JellyTitan/Sofle-Pico/docs/images/qmk/sofle_pico_hero_image.jpeg

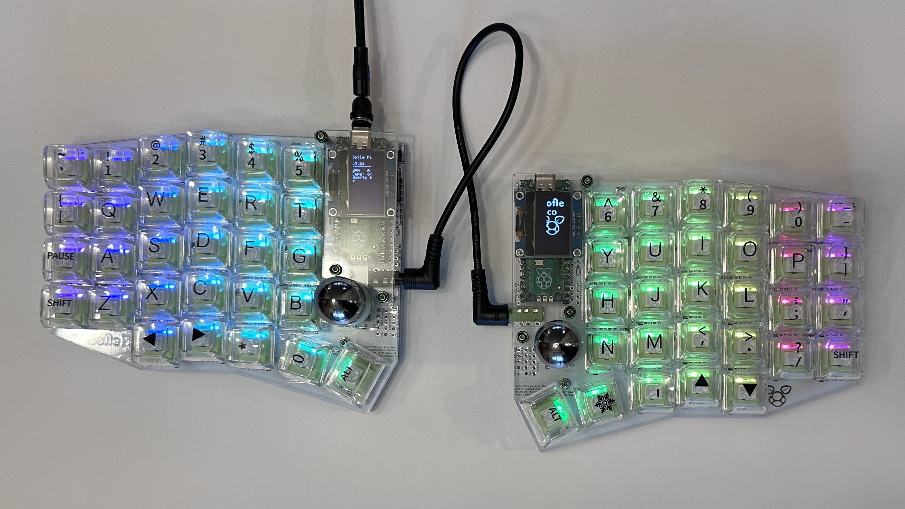
docs/images/qmk/sofle_pico_hero_image.jpeg
