JellyTitan/Sofle-Pico/docs/images/pcba_ordering_images/pcba_1.png

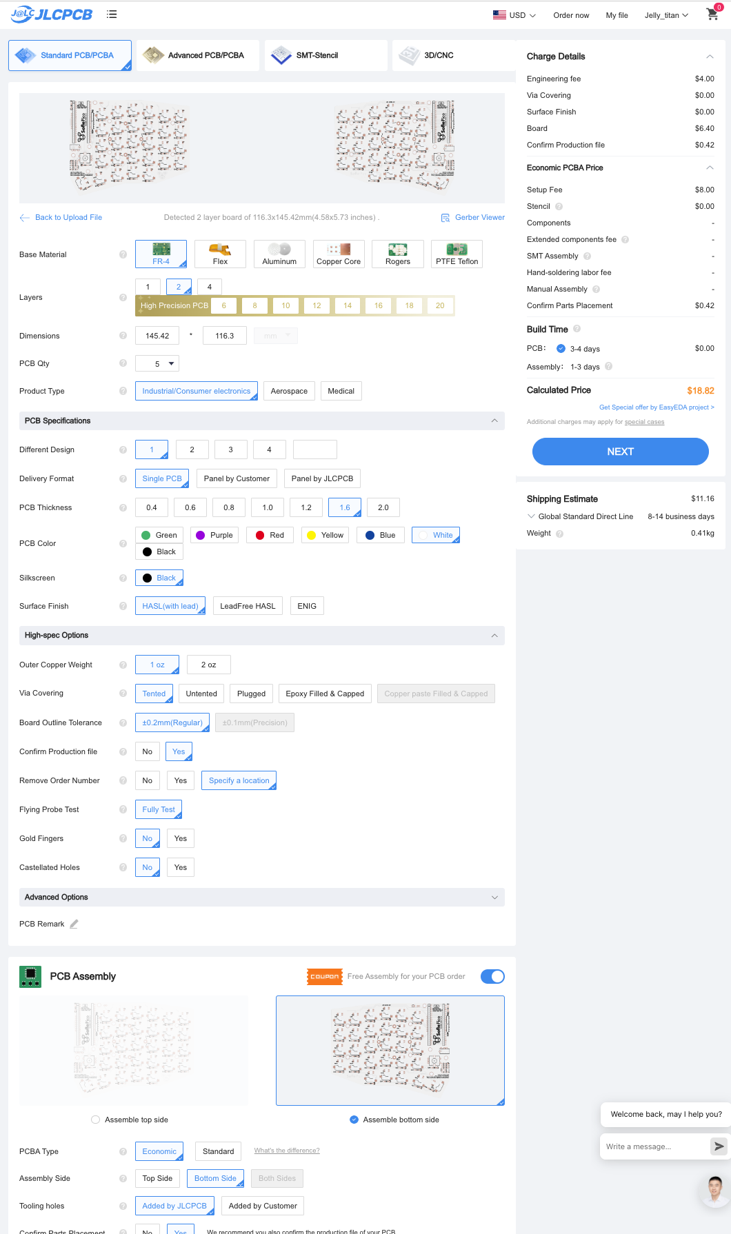
docs/images/pcba_ordering_images/pcba_1.png
