JellyTitan/Sofle-Pico/docs/images/pcba_ordering_images/pcba_3.png

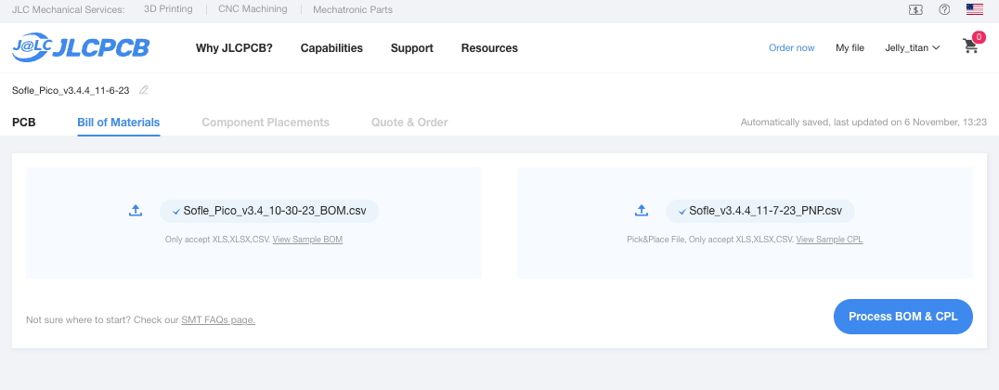
docs/images/pcba_ordering_images/pcba_3.png
