JellyTitan/Sofle-Pico/docs/images/pcba_ordering_images/pcba_4.png

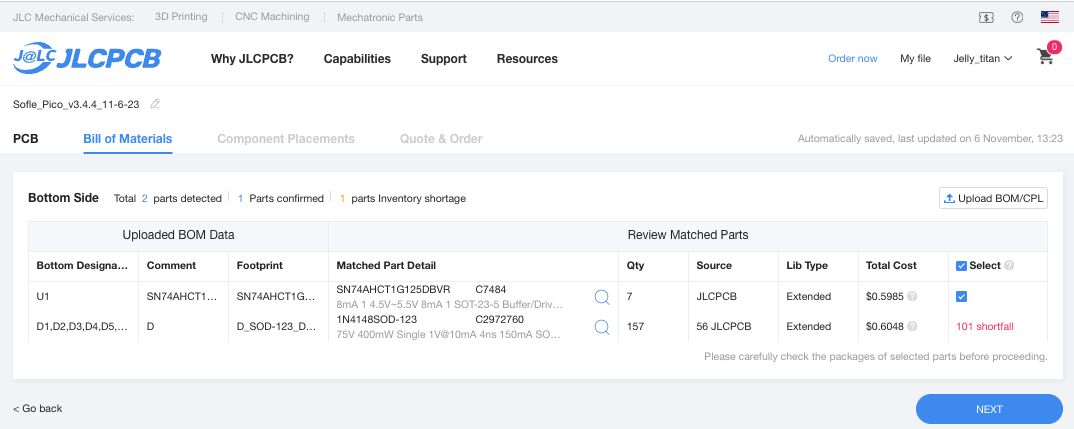
docs/images/pcba_ordering_images/pcba_4.png
