JellyTitan/Sofle-Pico/docs/images/pcba_ordering_images/pcba_5.png

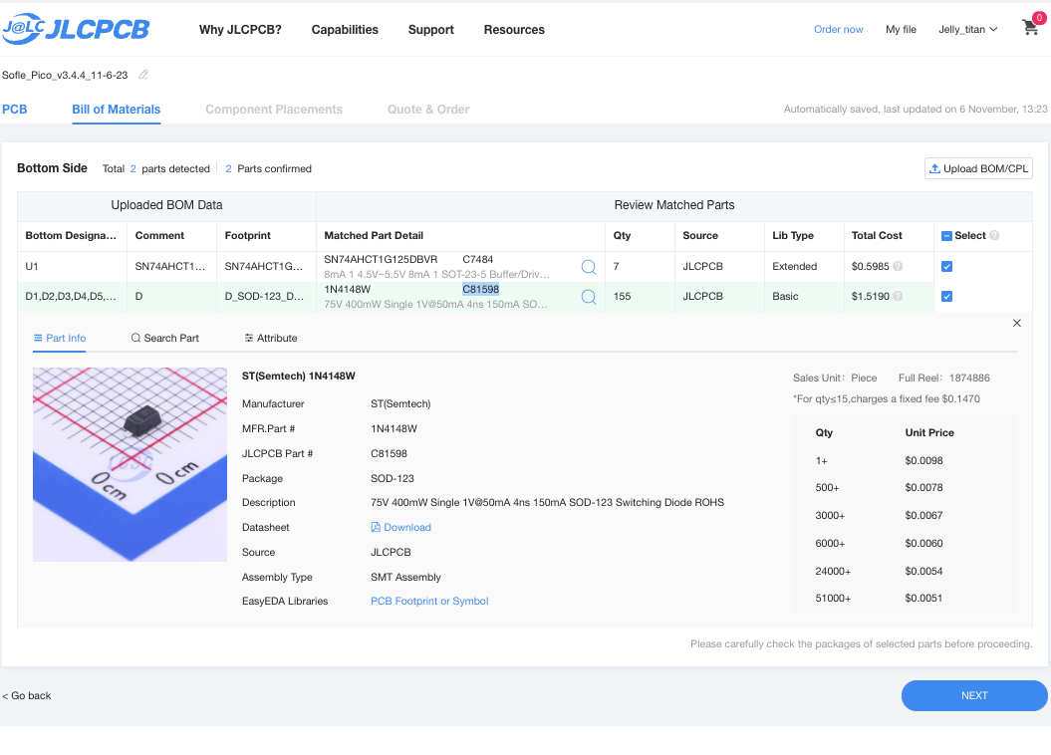
docs/images/pcba_ordering_images/pcba_5.png
