JellyTitan/Sofle-Pico/docs/images/pcba_ordering_images/pcba_6.png

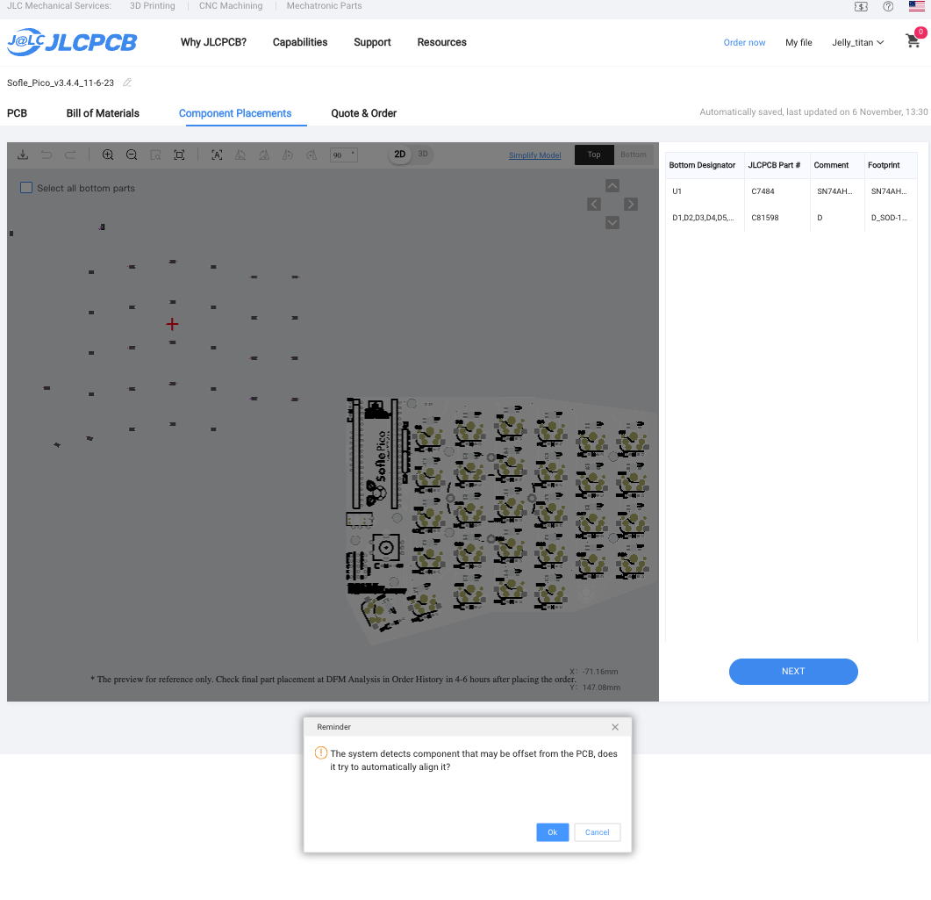
docs/images/pcba_ordering_images/pcba_6.png
