JellyTitan/Sofle-Pico/docs/images/pcba_ordering_images/pcba_7.png

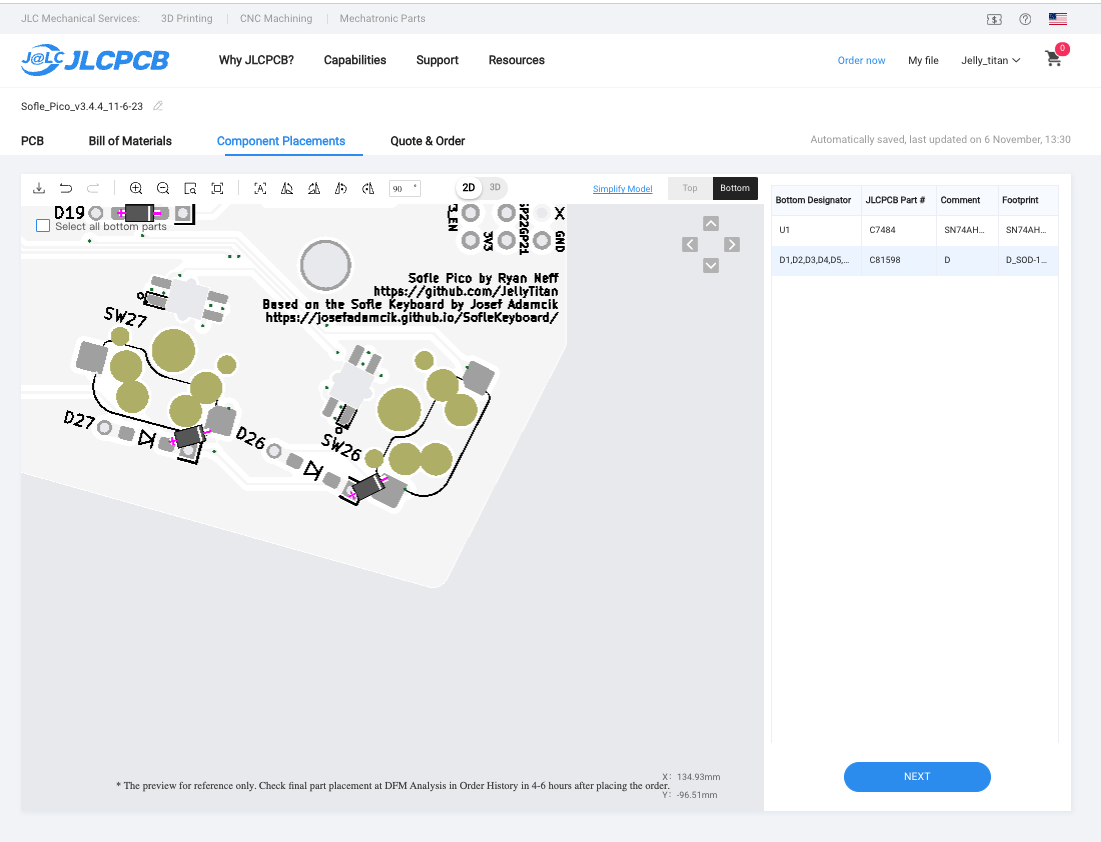
docs/images/pcba_ordering_images/pcba_7.png
