JellyTitan/Sofle-Pico/docs/images/pcba_ordering_images/pcba_8.png

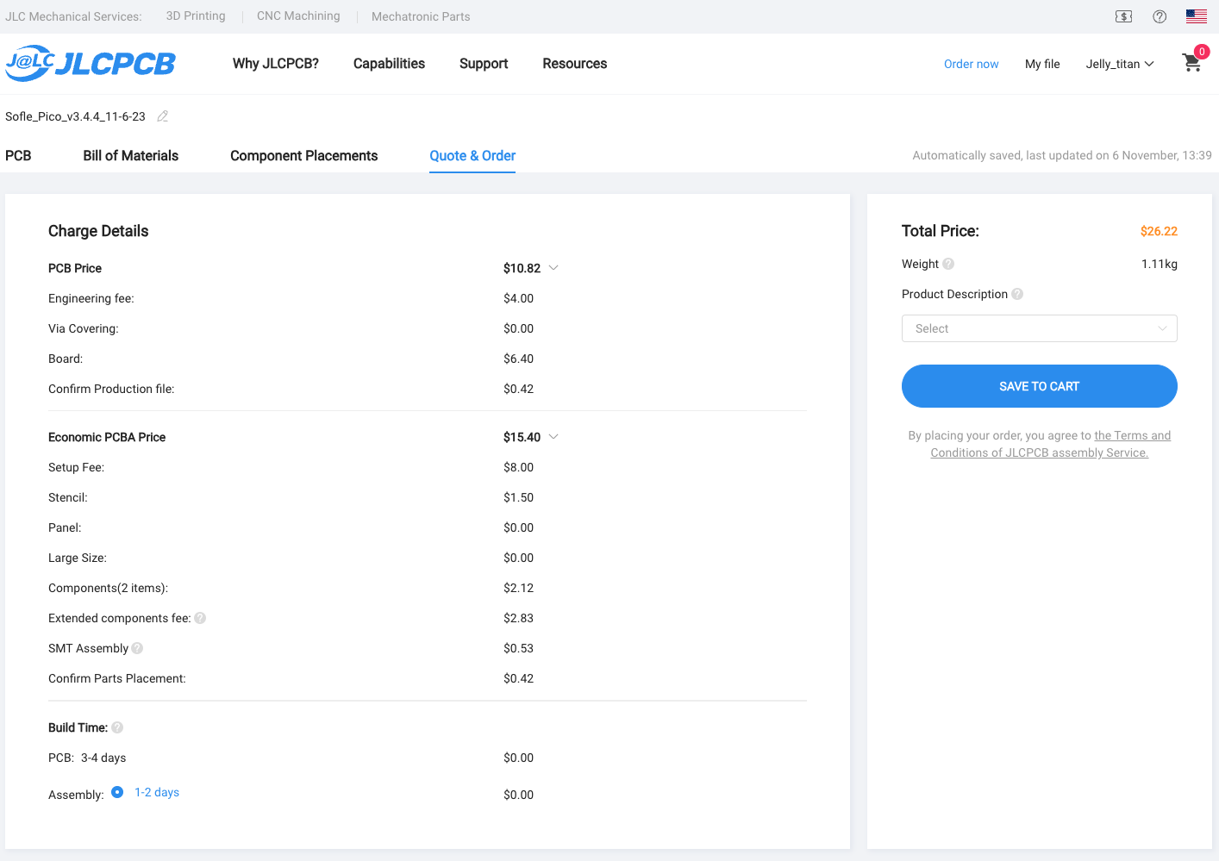
docs/images/pcba_ordering_images/pcba_8.png
