JellyTitan/Sofle-Pico/docs/images/pcba_ordering_images/pcba_9.png

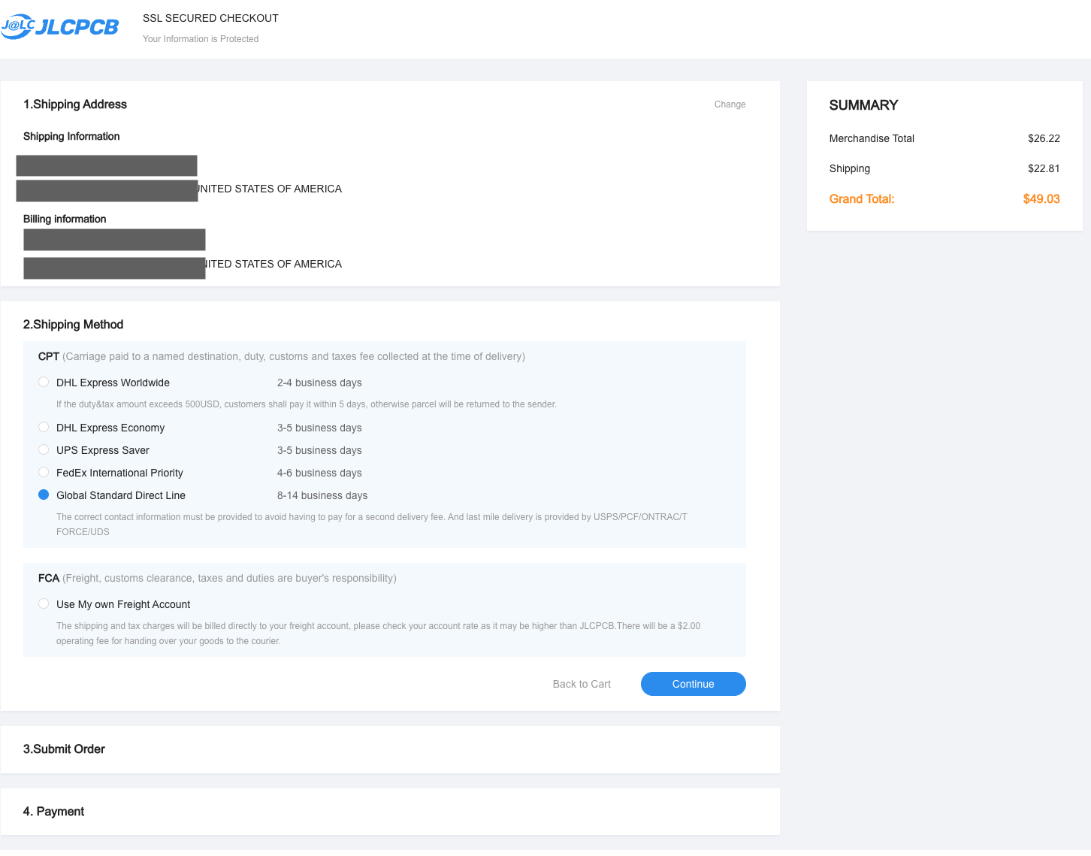
docs/images/pcba_ordering_images/pcba_9.png
