JellyTitan/Sofle-Pico/docs/images/pcba_ordering_images/pcba_11.png

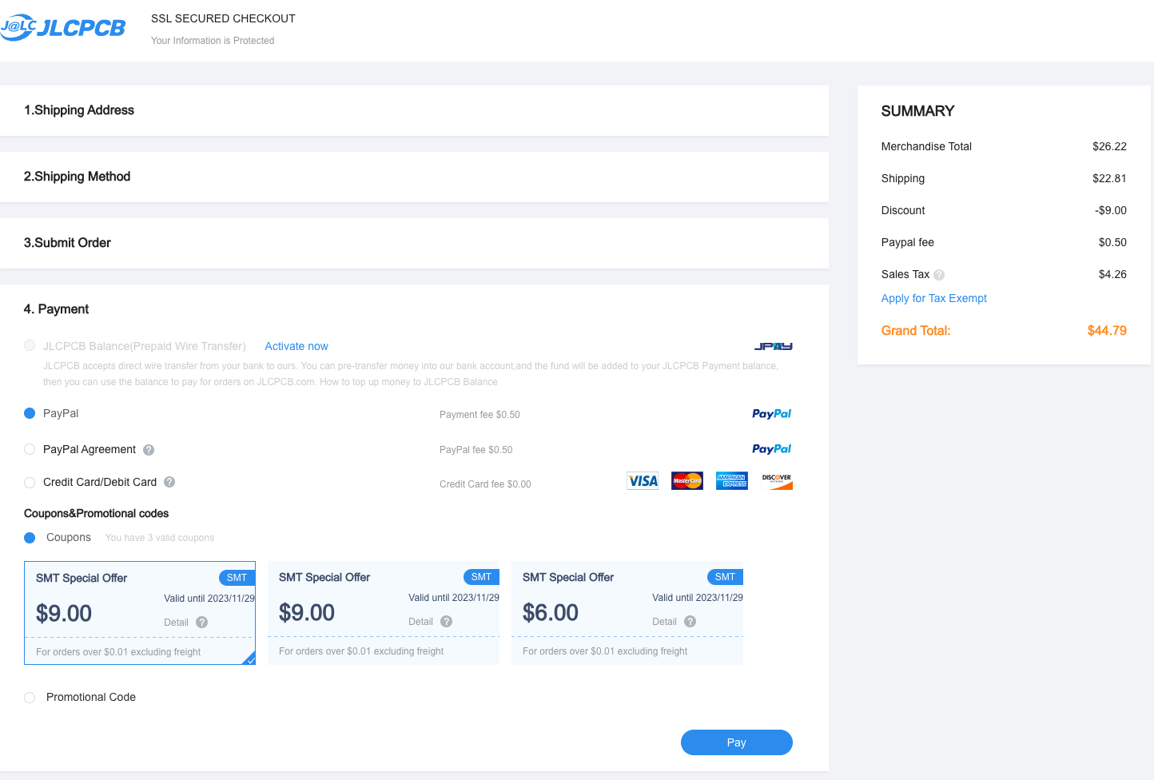
docs/images/pcba_ordering_images/pcba_11.png
