JellyTitan/Sofle-Pico/docs/images/pcba_ordering_images/Produce_DanZhi.SMT_Snapshot.Bottom.4539602A_Y61.SMT02311131475206.png

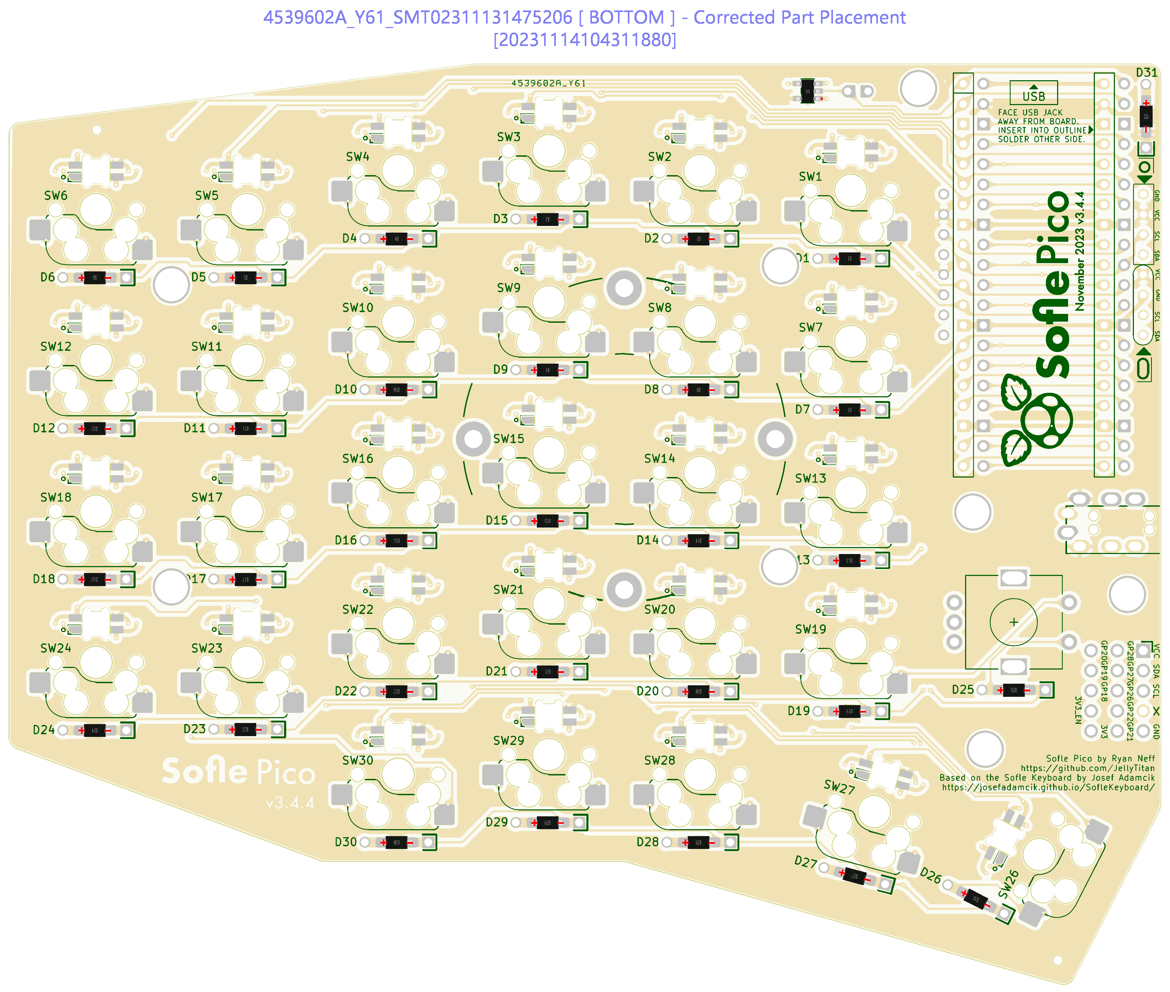
docs/images/pcba_ordering_images/Produce_DanZhi.SMT_Snapshot.Bottom.4539602A_Y61.SMT02311131475206.png
