JellyTitan/Sofle-Pico/docs/images/build_guide_pico/bending_jig.png

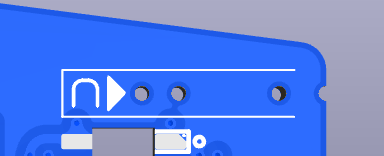
docs/images/build_guide_pico/bending_jig.png
