JellyTitan/Sofle-Pico/docs/images/build_guide_pico/sofle_pico_level_shifter.png

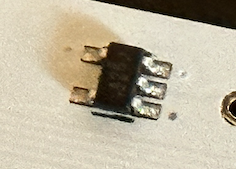
docs/images/build_guide_pico/sofle_pico_level_shifter.png
