JellyTitan/Sofle-Pico/docs/images/build_guide_pico/sofle_pico_tape.png

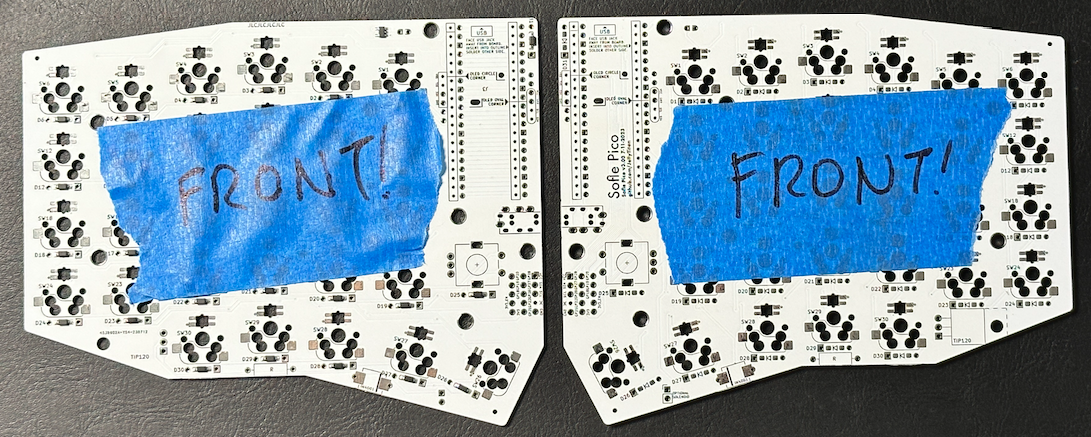
docs/images/build_guide_pico/sofle_pico_tape.png
