JellyTitan/Sofle-Pico/docs/images/build_guide_pico/sofle_pico_v3.3_hero.png

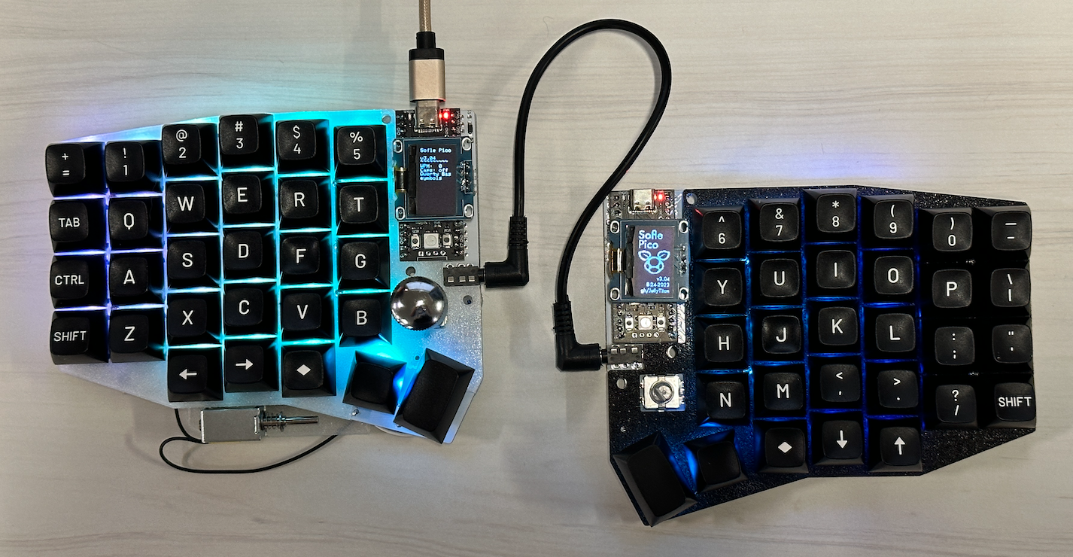
docs/images/build_guide_pico/sofle_pico_v3.3_hero.png
