JellyTitan/Sofle-Pico/docs/images/build_guide_pico/sofle_pico_v3.4.png

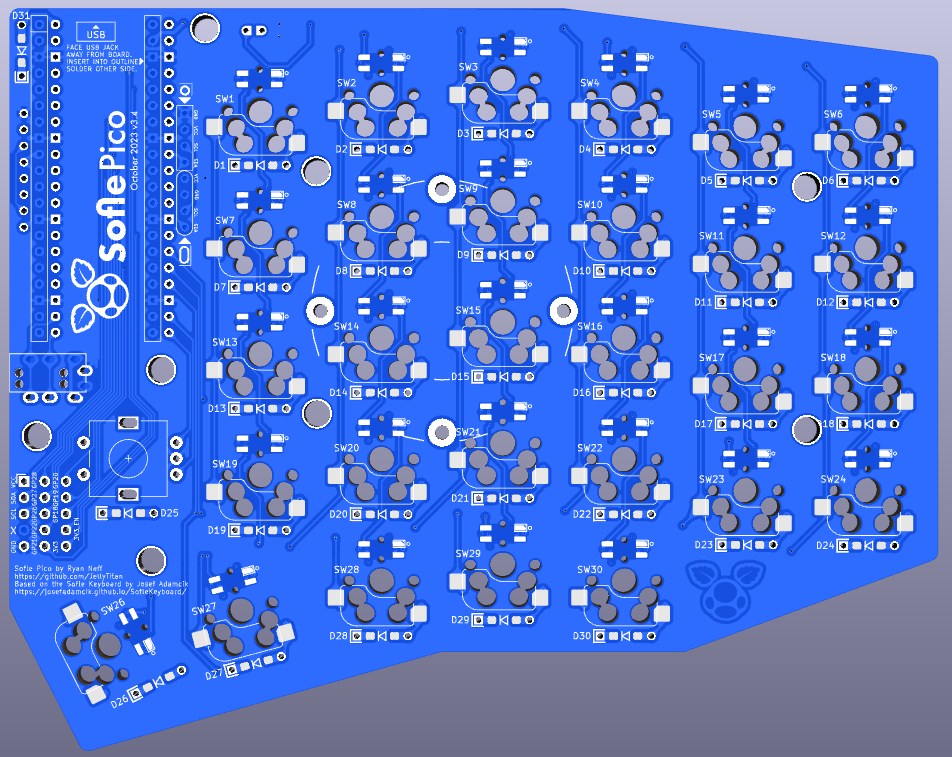
docs/images/build_guide_pico/sofle_pico_v3.4.png
