JellyTitan/Sofle-Pico/docs/images/build_guide_pico/sofle_v3_outline.png

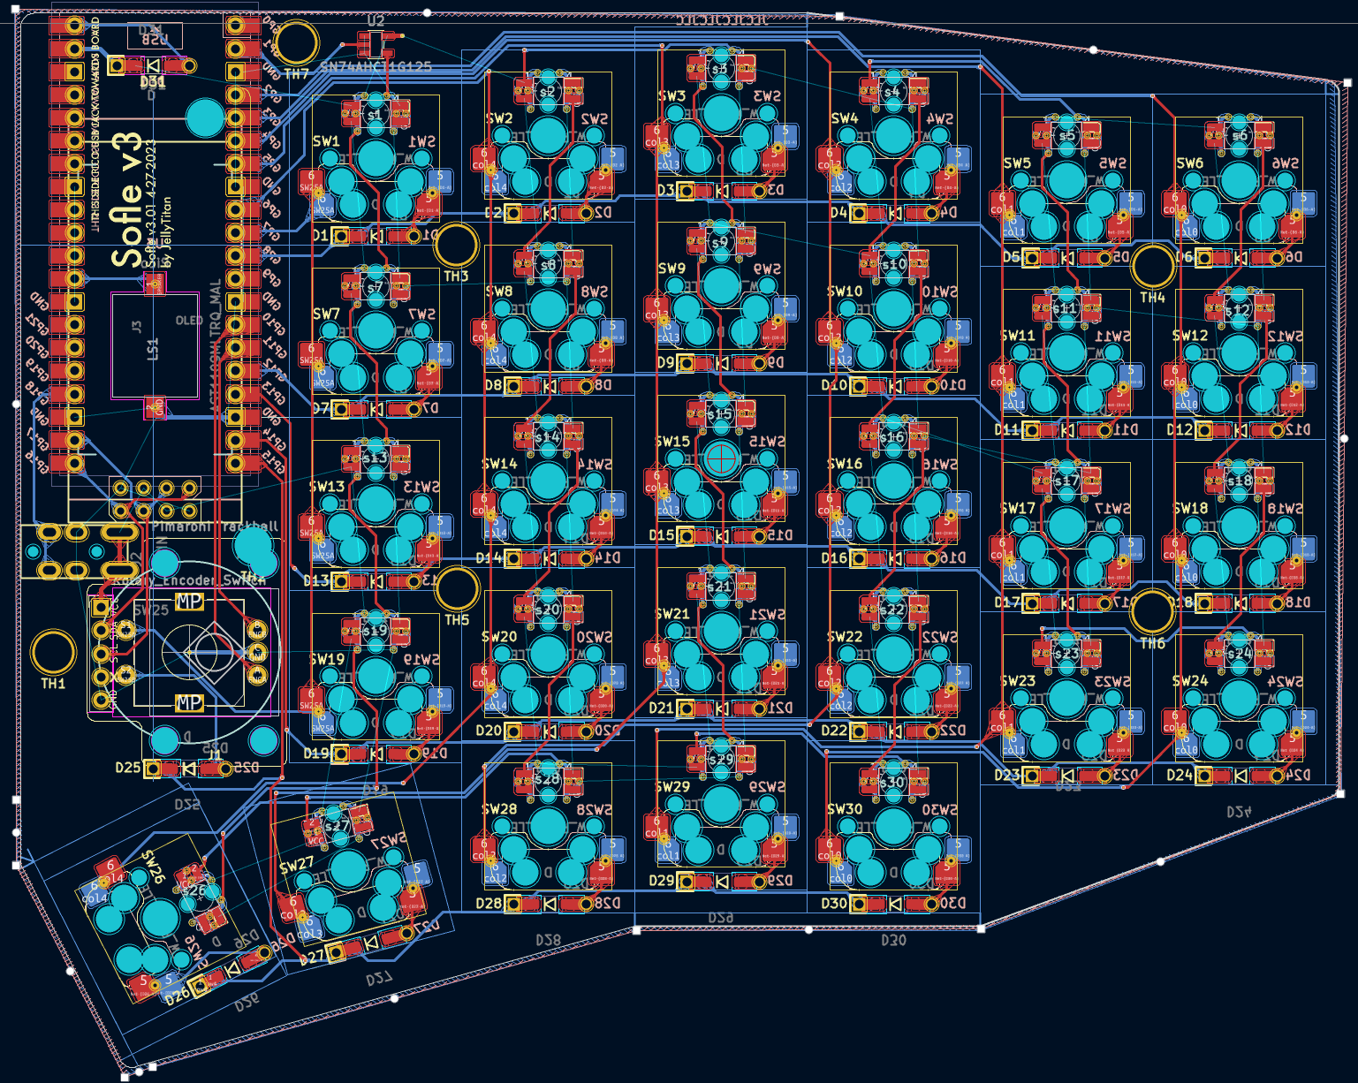
docs/images/build_guide_pico/sofle_v3_outline.png
