JellyTitan/Sofle-Pico/docs/images/build_guide_pico/sofle_v3b.png

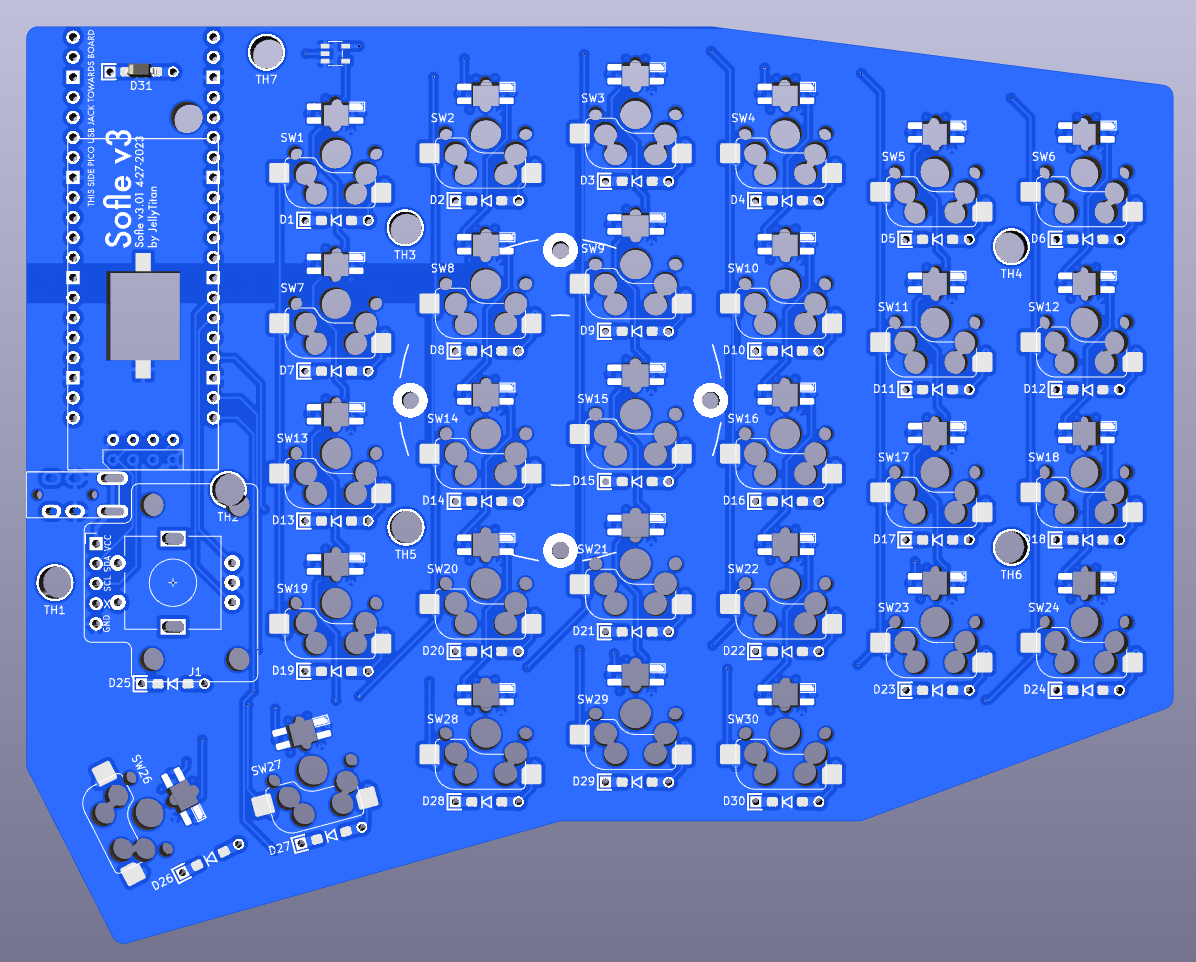
docs/images/build_guide_pico/sofle_v3b.png
