JellyTitan/Sofle-Pico/docs/images/ordering_guide/dumb_number_placement.png

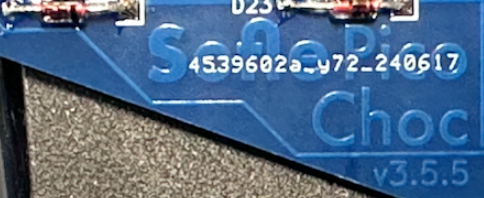
docs/images/ordering_guide/dumb_number_placement.png
