JellyTitan/Sofle-Pico/docs/images/build_log_pico/IR_00004.JPG

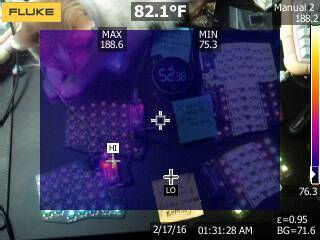
docs/images/build_log_pico/IR_00004.JPG
