JellyTitan/Sofle-Pico/Sofle_Pico/PCB/Sofle_Pico.kicad_sch

## KiCad design Sofle_Pico/PCB/Sofle_Pico.kicad_sch (2024-07-04)

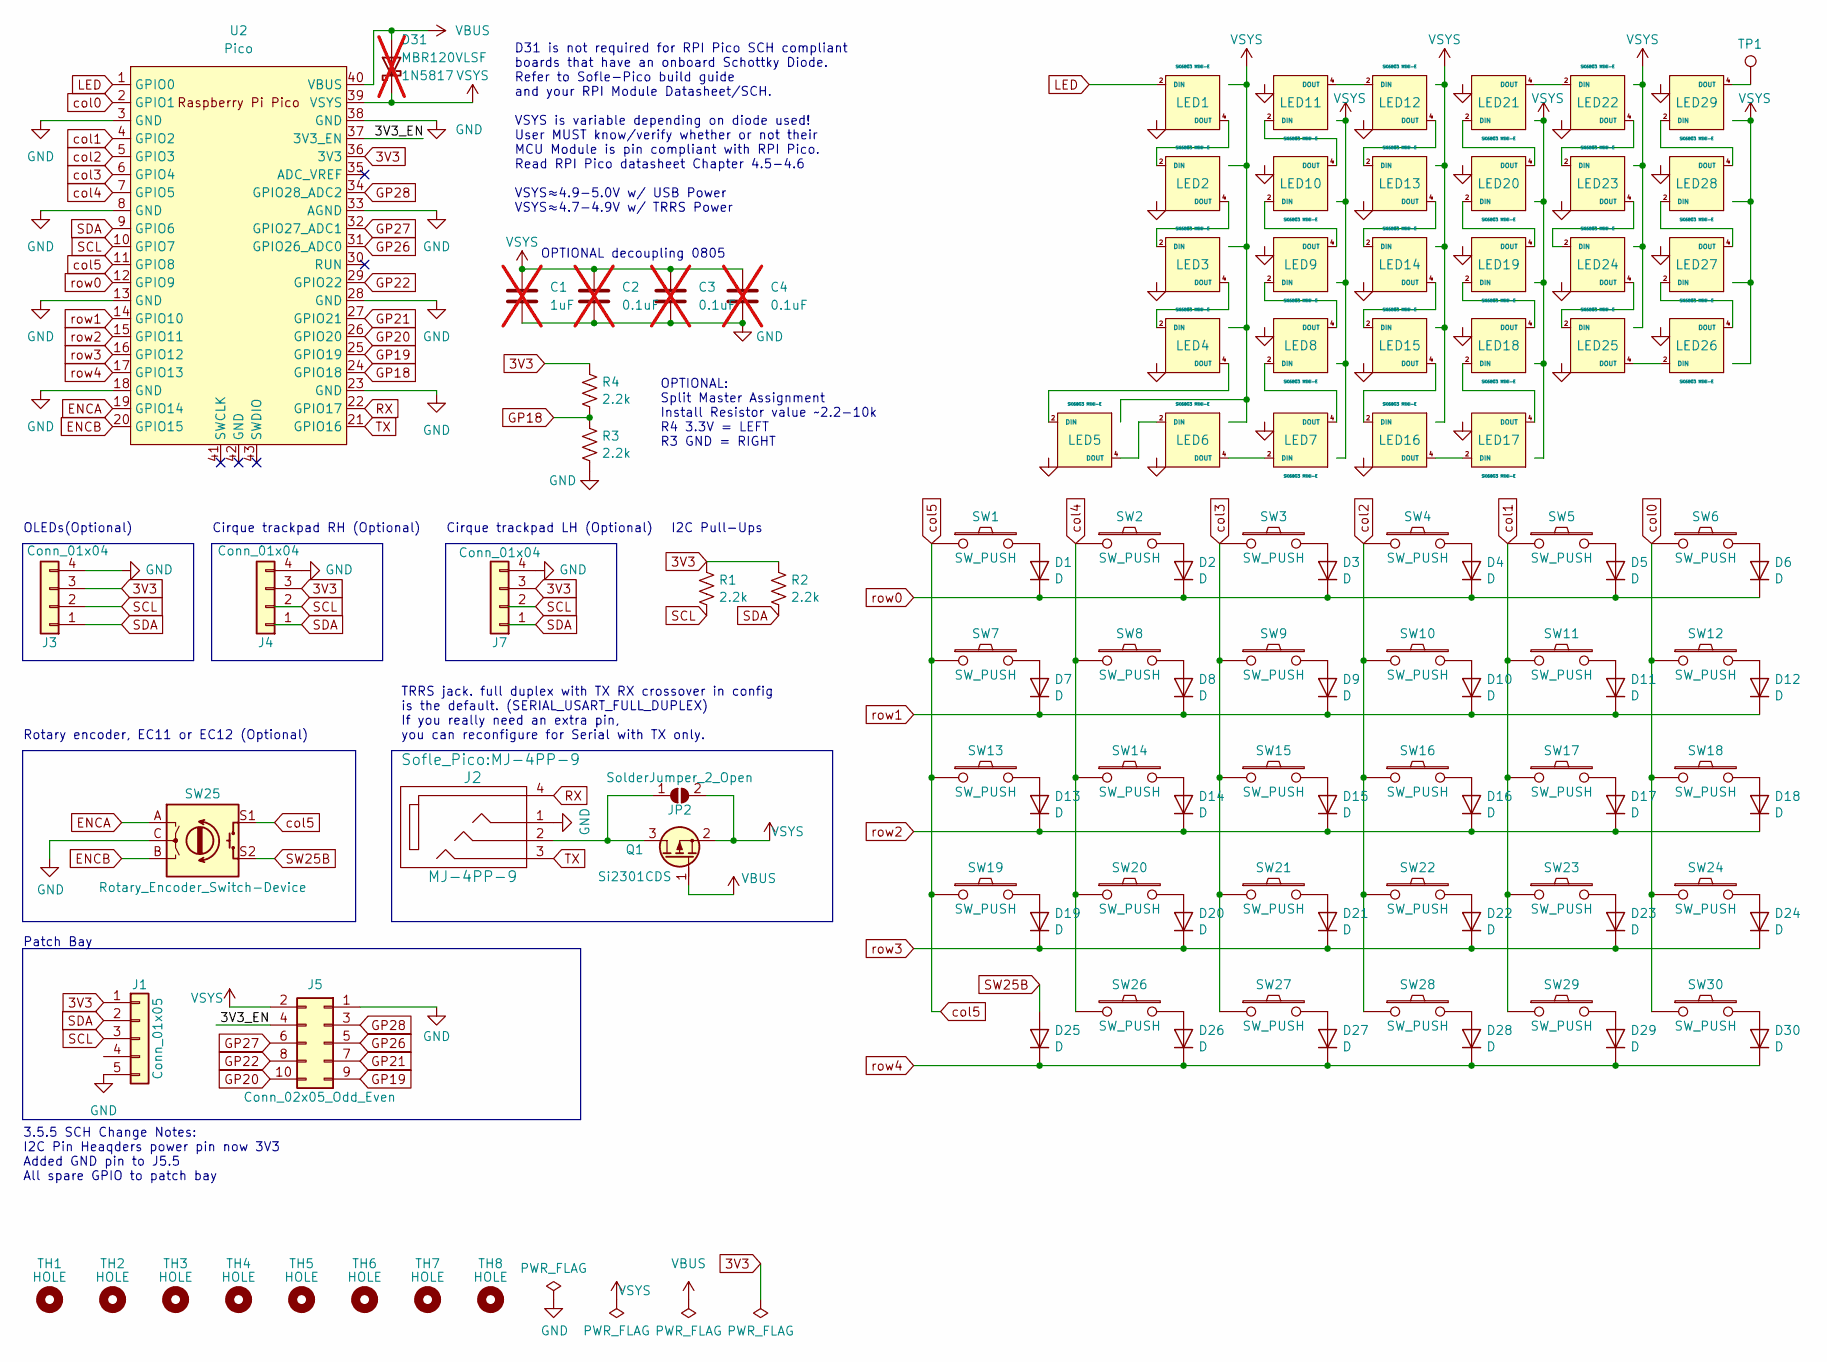
[picture p196: schematic Sofle_Pico.kicad_sch]

Parts:
C1: 1uF; C_0805_2012Metric_Pad1.18x1.45mm_HandSolder; Tolerance (%) 10; Voltage Rating 50V; MFG PN CL21B105KBFNNNE; JLCPCB_PN C28323; not fitted
C2, C3, C4: 0.1uF; C_0805_2012Metric_Pad1.18x1.45mm_HandSolder; Tolerance (%) 10; Voltage Rating 50V; MFG PN CC0805KRX7R9BB104; JLCPCB_PN C49678; not fitted
D1, D2, D3, D4, D5, D6, D7, D8, D9, D10, D11, D12, D13, D14, D15, D16, D17, D18, D19, D20, D21, D22, D23, D24, D25, D26, D27, D28, D29, D30: D; D_SOD-123_DO-35_Hybrid_DoubleSided_V2; Voltage Rating 75v; MFG PN 1N4148W; JLCPCB_PN C81598
D31: MBR120VLSF; D_SOD-123_DO-41_7.62mm_Hybrid_DoubleSided; not fitted
J1: Conn_01x05; Pimaroni_PinHeader_1x05_P2.54mm_Vertical Sofle v3b
J2: MJ-4PP-9
J3: Conn_01x04; OLED SSD1306 128x64
J4, J7: Conn_01x04; Cirque tie in
J5: Conn_02x05_Odd_Even; PinHeader_2x05_P2.54mm_Vertical
JP2: SolderJumper_2_Open; Level Shifter Bypass Jumper
LED1, LED2, LED3, LED4, LED5, LED6, LED7, LED8, LED9, LED10, LED11, LED12, LED13, LED14, LED15, LED16, LED17, LED18, LED19, LED20, LED21, LED22, LED23, LED24, LED25, LED26, LED27, LED28, LED29: SK6803 MINI-E; SK6803_MINI-E_v3.5.5
Q1: Si2301CDS; SOT-23; JLCPCB_PN C10487
R1, R2, R3, R4: 2.2k; Res_1206_SMD_6.3mm_TH_Hybrid
SW1, SW2, SW3, SW4, SW5, SW6, SW7, SW8, SW9, SW10, SW11, SW12, SW13, SW14, SW15, SW16, SW17, SW18, SW19, SW20, SW21, SW22, SW23, SW24, SW26, SW27, SW28, SW29, SW30: SW_PUSH; Cherry_MX_DS_Hotswap_v3.5.4
SW25: Rotary_Encoder_Switch-Device; RotaryEncoder_Alps_EC11E-Switch_Vertical_H20mm-keebio_modif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
TH1, TH2, TH7: HOLE; Hole from sofle for M2 posts gold rimmer wide-keyplate-hole
TH3, TH4, TH5, TH6, TH8: HOLE; Hole from sofle for M2 posts gold rimmer
TP1: TestPoint; TestPoint_THTPad_2.0x2.0mm_Drill1.0mm; JLCPCB_PN C94111
U2: Pico; RPi_Pico_SMD_TH_DS

Connections:
3V3: J1.1, J3.3, J4.3, J7.3, R1.1, R2.1, R4.2, U2.36 (3V3)
3V3_EN: J5.4, U2.37 (3V3_EN)
ENCA: SW25.A, U2.19 (GPIO14)
ENCB: SW25.B, U2.20 (GPIO15)
GND: C1.2, C2.2, C3.2, C4.2, J1.5, J2.1, J3.4, J4.4, J5.1, J7.4, LED1.1 (GND), LED2.1 (GND), LED3.1 (GND), LED4.1 (GND), LED5.1 (GND), LED6.1 (GND), LED7.1 (GND), LED8.1 (GND), LED9.1 (GND), LED10.1 (GND), LED11.1 (GND), LED12.1 (GND), LED13.1 (GND), LED14.1 (GND), LED15.1 (GND), LED16.1 (GND), LED17.1 (GND), LED18.1 (GND), LED19.1 (GND), LED20.1 (GND), LED21.1 (GND), LED22.1 (GND), LED23.1 (GND), LED24.1 (GND), LED25.1 (GND), LED26.1 (GND), LED27.1 (GND), LED28.1 (GND), LED29.1 (GND), R3.2, SW25.C, U2.3 (GND), U2.8 (GND), U2.13 (GND), U2.18 (GND), U2.23 (GND), U2.28 (GND), U2.33 (AGND), U2.38 (GND)
GP18: R3.1, R4.1, U2.24 (GPIO18)
GP19: J5.9, U2.25 (GPIO19)
GP20: J5.10, U2.26 (GPIO20)
GP21: J5.7, U2.27 (GPIO21)
GP22: J5.8, U2.29 (GPIO22)
GP26: J5.5, U2.31 (GPIO26_ADC0)
GP27: J5.6, U2.32 (GPIO27_ADC1)
GP28: J5.3, U2.34 (GPIO28_ADC2)
LED: LED1.2 (DIN), U2.1 (GPIO0)
unnamed: D1.2 (A), SW1.2
unnamed: D2.2 (A), SW2.2
unnamed: D3.2 (A), SW3.2
unnamed: D4.2 (A), SW4.2
unnamed: D5.2 (A), SW5.2
unnamed: D6.2 (A), SW6.2
unnamed: D7.2 (A), SW7.2
unnamed: D8.2 (A), SW8.2
unnamed: D9.2 (A), SW9.2
unnamed: D10.2 (A), SW10.2
unnamed: D11.2 (A), SW11.2
unnamed: D12.2 (A), SW12.2
unnamed: D13.2 (A), SW13.2
unnamed: D14.2 (A), SW14.2
unnamed: D15.2 (A), SW15.2
unnamed: D16.2 (A), SW16.2
unnamed: D17.2 (A), SW17.2
unnamed: D18.2 (A), SW18.2
unnamed: D19.2 (A), SW19.2
unnamed: D20.2 (A), SW20.2
unnamed: D21.2 (A), SW21.2
unnamed: D22.2 (A), SW22.2
unnamed: D23.2 (A), SW23.2
unnamed: D24.2 (A), SW24.2
unnamed: D26.2 (A), SW26.1
unnamed: D27.2 (A), SW27.2
unnamed: D28.2 (A), SW28.2
unnamed: D29.2 (A), SW29.2
unnamed: D30.2 (A), SW30.2
unnamed: J2.2, JP2.1 (A), Q1.3 (D)
unnamed: LED1.4 (DOUT), LED2.2 (DIN)
unnamed: LED2.4 (DOUT), LED3.2 (DIN)
unnamed: LED3.4 (DOUT), LED4.2 (DIN)
unnamed: LED4.4 (DOUT), LED5.2 (DIN)
unnamed: LED5.4 (DOUT), LED6.2 (DIN)
unnamed: LED6.4 (DOUT), LED7.2 (DIN)
unnamed: LED7.4 (DOUT), LED8.2 (DIN)
unnamed: LED8.4 (DOUT), LED9.2 (DIN)
unnamed: LED9.4 (DOUT), LED10.2 (DIN)
unnamed: LED10.4 (DOUT), LED11.2 (DIN)
unnamed: LED11.4 (DOUT), LED12.2 (DIN)
unnamed: LED12.4 (DOUT), LED13.2 (DIN)
unnamed: LED13.4 (DOUT), LED14.2 (DIN)
unnamed: LED14.4 (DOUT), LED15.2 (DIN)
unnamed: LED15.4 (DOUT), LED16.2 (DIN)
unnamed: LED16.4 (DOUT), LED17.2 (DIN)
unnamed: LED17.4 (DOUT), LED18.2 (DIN)
unnamed: LED18.4 (DOUT), LED19.2 (DIN)
unnamed: LED19.4 (DOUT), LED20.2 (DIN)
unnamed: LED20.4 (DOUT), LED21.2 (DIN)
unnamed: LED21.4 (DOUT), LED22.2 (DIN)
unnamed: LED22.4 (DOUT), LED23.2 (DIN)
unnamed: LED23.4 (DOUT), LED24.2 (DIN)
unnamed: LED24.4 (DOUT), LED25.2 (DIN)
unnamed: LED25.4 (DOUT), LED26.2 (DIN)
unnamed: LED26.4 (DOUT), LED27.2 (DIN)
unnamed: LED27.4 (DOUT), LED28.2 (DIN)
unnamed: LED28.4 (DOUT), LED29.2 (DIN)
unnamed: LED29.4 (DOUT), TP1.1
RX: J2.4, U2.22 (GPIO17)
SCL: J1.3, J3.2, J4.2, J7.2, R1.2, U2.10 (GPIO7)
SDA: J1.2, J3.1, J4.1, J7.1, R2.2, U2.9 (GPIO6)
SW25B: D25.2 (A), SW25.S2
TX: J2.3, U2.21 (GPIO16)
VBUS: D31.2 (A), Q1.1 (G), U2.40 (VBUS)
VSYS: C1.1, C2.1, C3.1, C4.1, D31.1 (K), J5.2, JP2.2 (B), LED1.3 (VDD), LED2.3 (VDD), LED3.3 (VDD), LED4.3 (VDD), LED5.3 (VDD), LED6.3 (VDD), LED7.3 (VDD), LED8.3 (VDD), LED9.3 (VDD), LED10.3 (VDD), LED11.3 (VDD), LED12.3 (VDD), LED13.3 (VDD), LED14.3 (VDD), LED15.3 (VDD), LED16.3 (VDD), LED17.3 (VDD), LED18.3 (VDD), LED19.3 (VDD), LED20.3 (VDD), LED21.3 (VDD), LED22.3 (VDD), LED23.3 (VDD), LED24.3 (VDD), LED25.3 (VDD), LED26.3 (VDD), LED27.3 (VDD), LED28.3 (VDD), LED29.3 (VDD), Q1.2 (S), U2.39 (VSYS)
col0: SW6.1, SW12.1, SW18.1, SW24.1, SW30.1, U2.2 (GPIO1)
col1: SW5.1, SW11.1, SW17.1, SW23.1, SW29.1, U2.4 (GPIO2)
col2: SW4.1, SW10.1, SW16.1, SW22.1, SW28.1, U2.5 (GPIO3)
col3: SW3.1, SW9.1, SW15.1, SW21.1, SW27.1, U2.6 (GPIO4)
col4: SW2.1, SW8.1, SW14.1, SW20.1, SW26.2, U2.7 (GPIO5)
col5: SW1.1, SW7.1, SW13.1, SW19.1, SW25.S1, U2.11 (GPIO8)
row0: D1.1 (K), D2.1 (K), D3.1 (K), D4.1 (K), D5.1 (K), D6.1 (K), U2.12 (GPIO9)
row1: D7.1 (K), D8.1 (K), D9.1 (K), D10.1 (K), D11.1 (K), D12.1 (K), U2.14 (GPIO10)
row2: D13.1 (K), D14.1 (K), D15.1 (K), D16.1 (K), D17.1 (K), D18.1 (K), U2.15 (GPIO11)
row3: D19.1 (K), D20.1 (K), D21.1 (K), D22.1 (K), D23.1 (K), D24.1 (K), U2.16 (GPIO12)
row4: D25.1 (K), D26.1 (K), D27.1 (K), D28.1 (K), D29.1 (K), D30.1 (K), U2.17 (GPIO13)

Notes on the sheet:
Cirque trackpad RH (Optional)
I2C Pull-Ups
TRRS jack. full duplex with TX RX crossover in config is the default. (SERIAL_USART_FULL_DUPLEX) If you really need an extra pin, you can reconfigure for Serial with TX only.
Rotary encoder, EC11 or EC12 (Optional)
D31 is not required for RPI Pico SCH compliant boards that have an onboard Schottky Diode. Refer to Sofle-Pico build guide and your RPI Module Datasheet/SCH. VSYS is variable depending on diode used! User MUST know/verify whether or not their MCU Module is pin compliant with RPI Pico. Read RPI Pico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
OPTIONAL: Split Master Assignment Install Resistor value ~2.2-10k R4 3.3V = LEFT R3 GND = RIGHT
OLEDs(Optional)
Patch Bay
Cirque trackpad LH (Optional)
OPTIONAL decoupling 0805
3.5.5 SCH Change Notes: I2C Pin Heaqders power pin now 3V3 Added GND pin to J5.5 All spare GPIO to patch bay
